MatterOfTechnologies/PiLC/Useful Code/Python/single_mcp3004_read.py

import time
import sys
# Import SPI library (for hardware SPI) and MCP3008 library.
import Adafruit_GPIO.SPI as SPI
import Adafruit_MCP3008

# Hardware SPI configuration:
SPI_PORT   = 0
SPI_DEVICE = 0
mcp = Adafruit_MCP3008.MCP3008(spi=SPI.SpiDev(SPI_PORT, SPI_DEVICE))

i = int(sys.argv[1])
print(mcp.read_adc(i))
